vektorious/smart_home_sensor/instructions/img/device_hero.jpeg

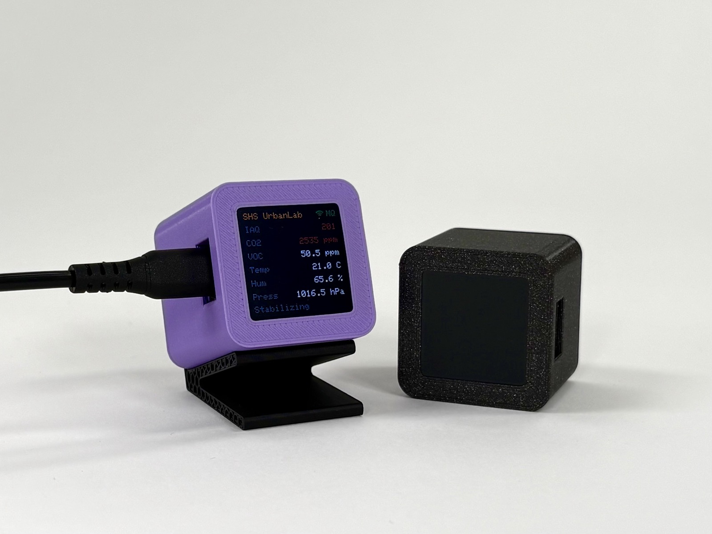
instructions/img/device_hero.jpeg
