vektorious/smart_home_sensor/code/shs_modular/bsec_config_33v_3s_4d.h

// BSEC config blob: BME680, IAQ, 3.3 V supply, LP (3 s) sample rate,
// 4-day calibration window  (bme680_iaq_33v_3s_4d/bsec_iaq.txt).
// Generated from the bsec2 library; pass to envSensor.setConfig().
#pragma once
#include <stdint.h>

const uint8_t bsec_config_iaq[] = {
0,1,6,2,189,1,0,0,0,0,0,0,127,7,0,0,56,0,1,0,0,192,168,71,64,49,119,76,0,0,97,69,0,0,97,69,10,0,3,0,0,0,96,64,23,183,209,56,43,24,149,60,140,74,106,188,43,24,149,60,216,129,243,190,151,255,80,190,216,129,243,190,8,0,2,0,0,0,72,66,16,0,3,0,10,215,163,60,10,215,35,59,10,215,35,59,13,0,5,0,0,0,0,0,100,35,41,29,86,88,0,9,0,229,208,34,62,0,0,0,0,0,0,0,0,218,27,156,62,225,11,67,64,0,0,160,64,0,0,0,0,0,0,0,0,94,75,72,189,93,254,159,64,66,62,160,191,0,0,0,0,0,0,0,0,33,31,180,190,138,176,97,64,65,241,99,190,0,0,0,0,0,0,0,0,167,121,71,61,165,189,41,192,184,30,189,64,12,0,10,0,0,0,0,0,0,0,0,0,45,5,11,0,1,1,2,0,0,0,0,0,0,0,0,0,0,0,0,0,0,0,0,0,0,0,0,0,0,0,0,0,0,0,0,0,0,0,0,0,0,0,0,0,0,0,0,0,0,0,0,0,0,0,0,0,0,0,0,0,0,0,0,0,0,0,0,0,0,0,0,0,0,0,0,0,0,0,0,0,0,0,0,0,0,0,0,0,0,0,0,0,0,0,0,0,0,0,0,0,0,0,0,0,0,128,63,0,0,128,63,0,0,128,63,0,0,128,63,0,0,128,63,0,0,128,63,0,0,128,63,0,0,128,63,0,0,128,63,0,0,128,63,0,0,128,63,0,0,128,63,0,0,128,63,0,0,128,63,0,0,128,63,0,0,128,63,0,0,128,63,0,0,128,63,0,0,128,63,0,0,128,63,0,0,128,63,0,0,128,63,0,0,128,63,0,0,128,63,0,0,128,63,0,0,128,63,0,0,128,63,0,0,128,63,0,0,128,63,0,0,128,63,0,0,128,63,0,0,128,63,0,0,128,63,0,0,128,63,0,0,128,63,0,0,128,63,0,0,128,63,0,0,128,63,0,0,128,63,0,0,128,63,0,0,128,63,0,0,128,63,0,0,128,63,0,0,128,63,0,0,128,63,0,0,128,63,0,0,128,63,0,0,128,63,0,0,128,63,0,0,128,63,0,0,128,63,0,0,128,63,0,0,128,63,0,0,128,63,0,0,128,63,0,0,128,63,0,0,128,63,0,0,128,63,0,0,128,63,0,0,128,63,0,0,128,63,0,0,128,63,0,0,128,63,0,0,128,63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
};
